mattywausb/ElBanquos_ChristmasLight/Documentation/demo_pictures/01_snowman.jpg

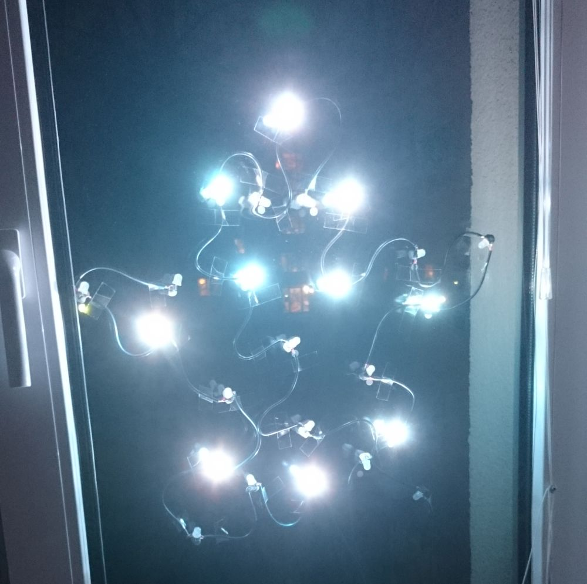
Documentation/demo_pictures/01_snowman.jpg
