mattywausb/ElBanquos_ChristmasLight/Documentation/demo_pictures/02_tree.jpg

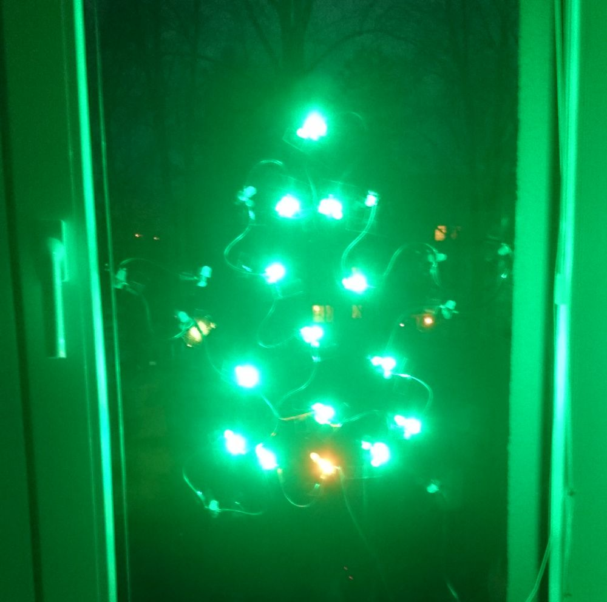
Documentation/demo_pictures/02_tree.jpg
