mattywausb/ElBanquos_ChristmasLight/Documentation/demo_pictures/03_star.jpg

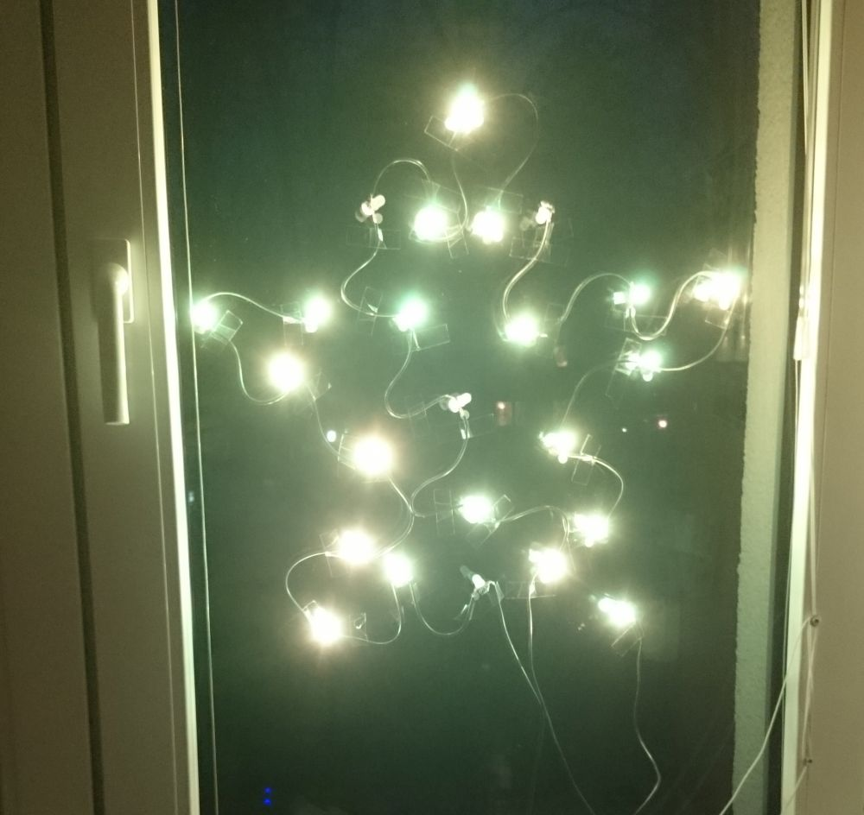
Documentation/demo_pictures/03_star.jpg
