mattywausb/ElBanquos_ChristmasLight/Documentation/demo_pictures/04_heart.jpg

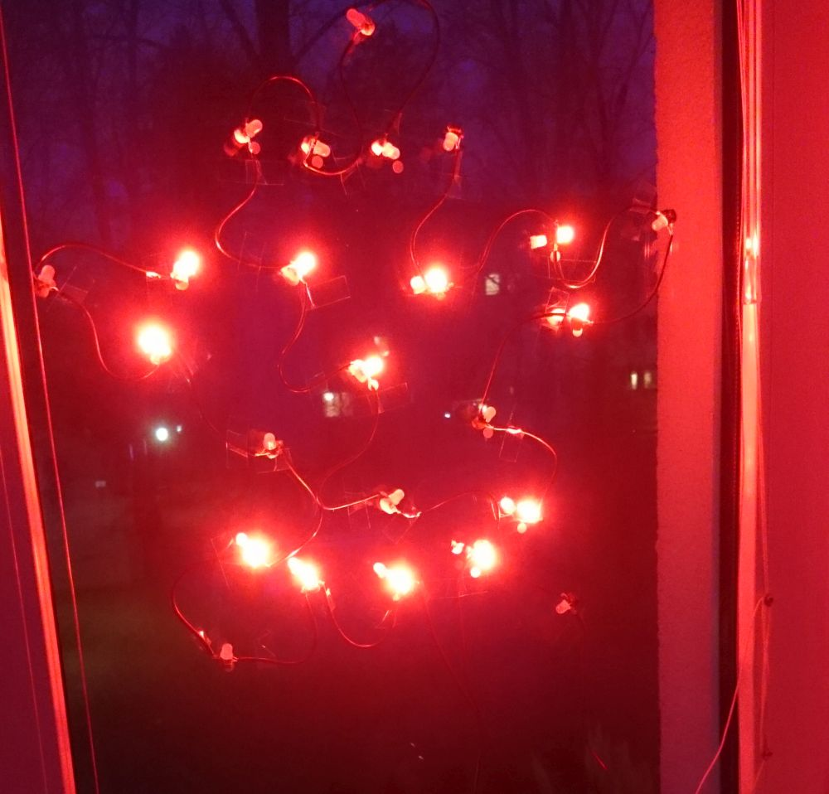
Documentation/demo_pictures/04_heart.jpg
