mattywausb/ElBanquos_ChristmasLight/Documentation/lampArrangement.png

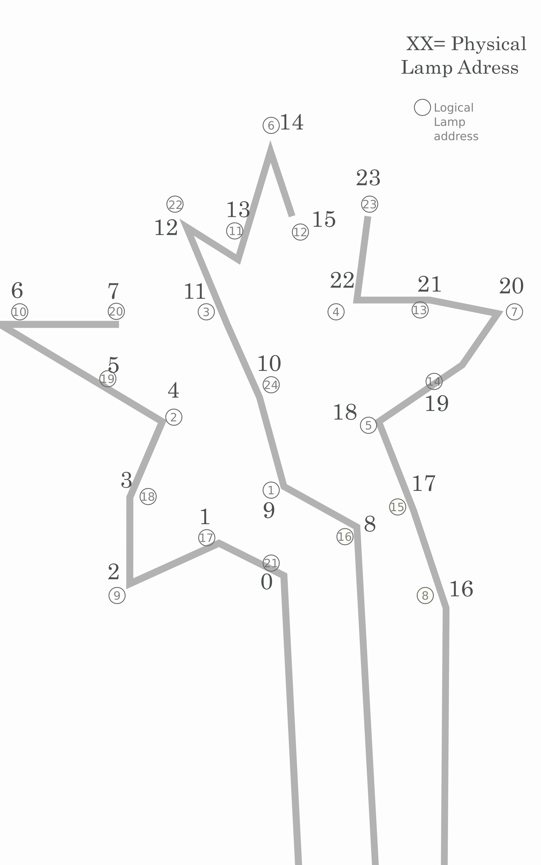
Documentation/lampArrangement.png
