mattywausb/ElBanquos_ChristmasLight/Documentation/build_pictures/02_multicore_cables_from_pc_junkyard.jpg

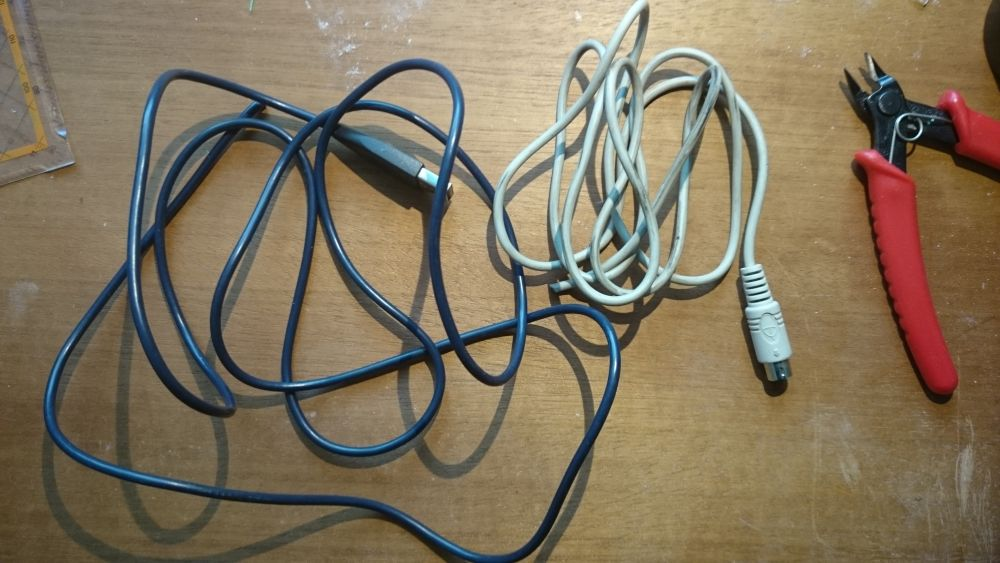
Documentation/build_pictures/02_multicore_cables_from_pc_junkyard.jpg
