mattywausb/ElBanquos_ChristmasLight/Documentation/build_pictures/05_final_wire_element.jpg

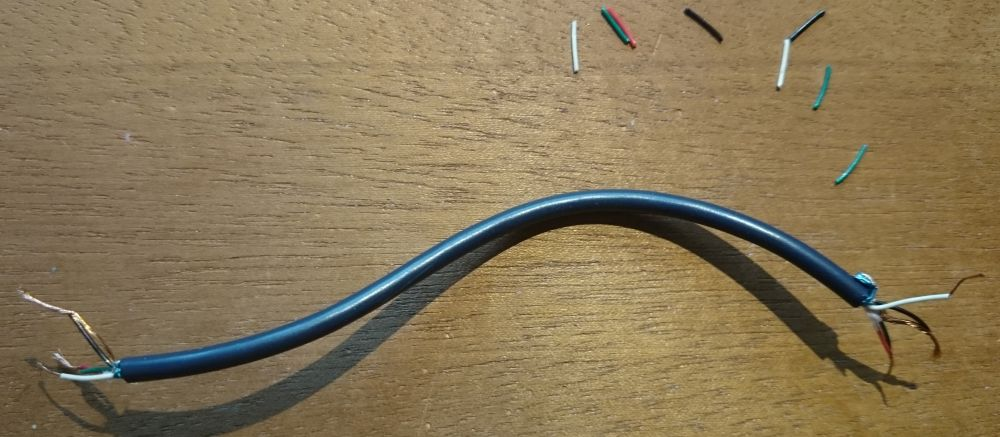
Documentation/build_pictures/05_final_wire_element.jpg
