mattywausb/ElBanquos_ChristmasLight/Documentation/build_pictures/06_ready_to_mount.jpg

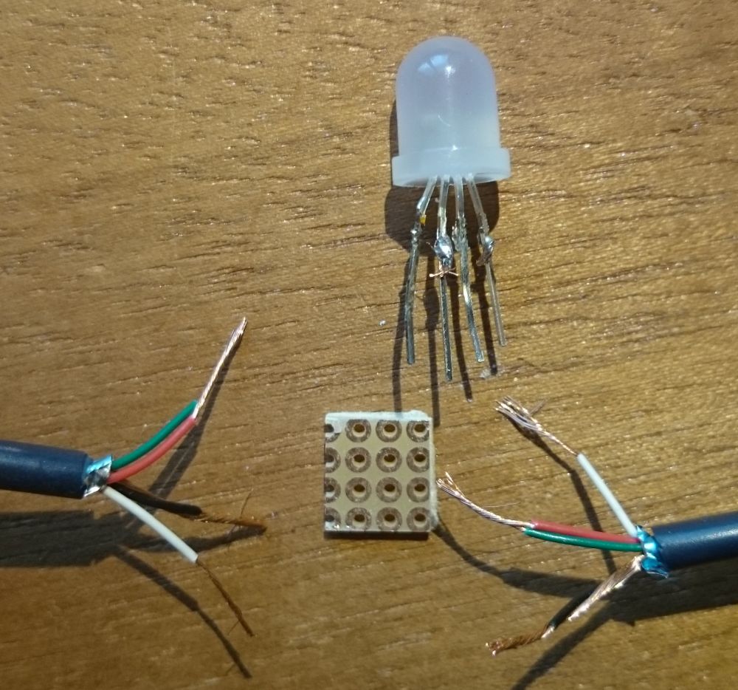
Documentation/build_pictures/06_ready_to_mount.jpg
