mattywausb/ElBanquos_ChristmasLight/Documentation/build_pictures/07_wires_first.jpg

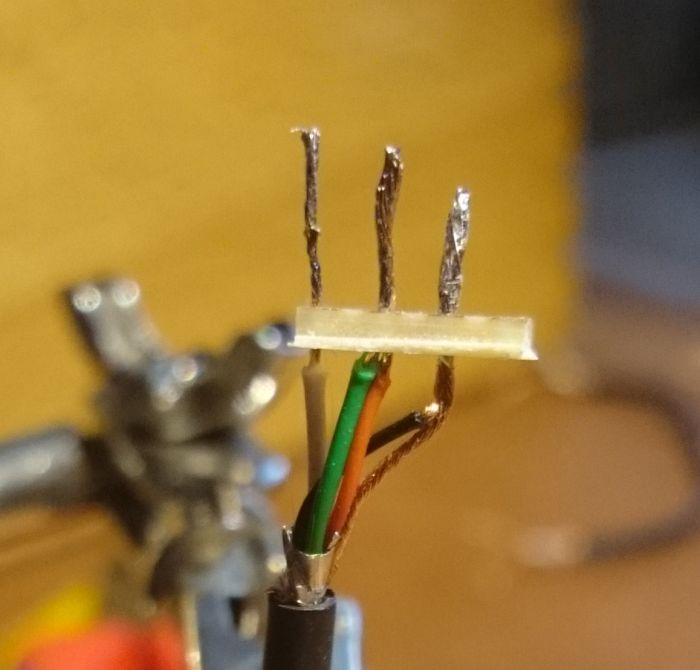
Documentation/build_pictures/07_wires_first.jpg
