mattywausb/ElBanquos_ChristmasLight/Documentation/build_pictures/08_wires_first_b.jpg

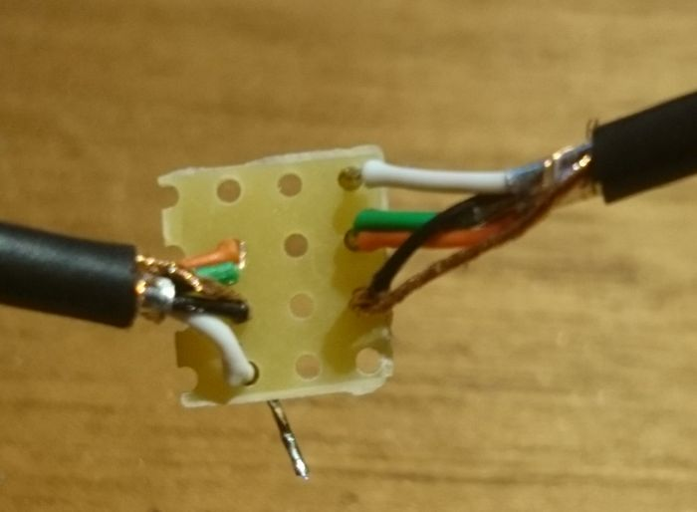
Documentation/build_pictures/08_wires_first_b.jpg
