mattywausb/ElBanquos_ChristmasLight/Documentation/build_pictures/09_bended_led_contacts.jpg

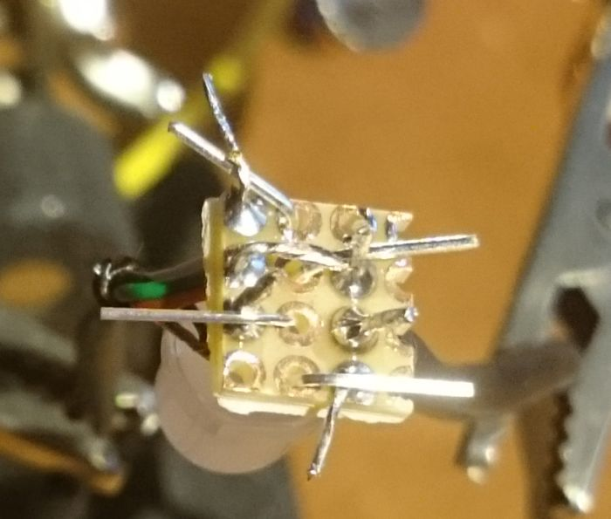
Documentation/build_pictures/09_bended_led_contacts.jpg
