mattywausb/ElBanquos_ChristmasLight/Documentation/build_pictures/10_solded_lamp.jpg

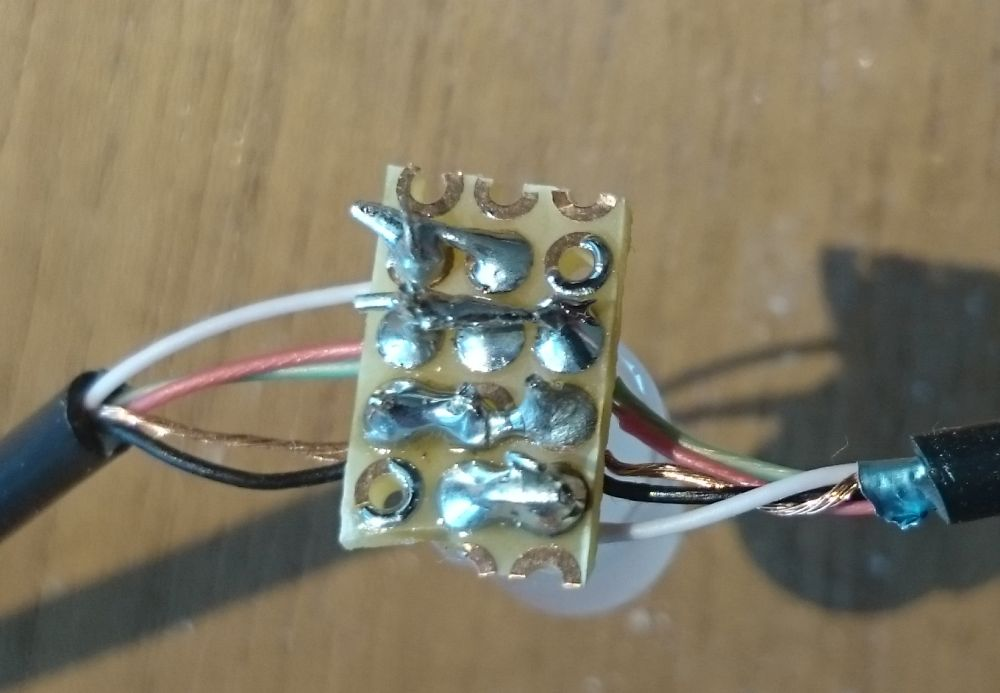
Documentation/build_pictures/10_solded_lamp.jpg
