mattywausb/ElBanquos_ChristmasLight/Documentation/build_pictures/11_final_lamp_element.jpg

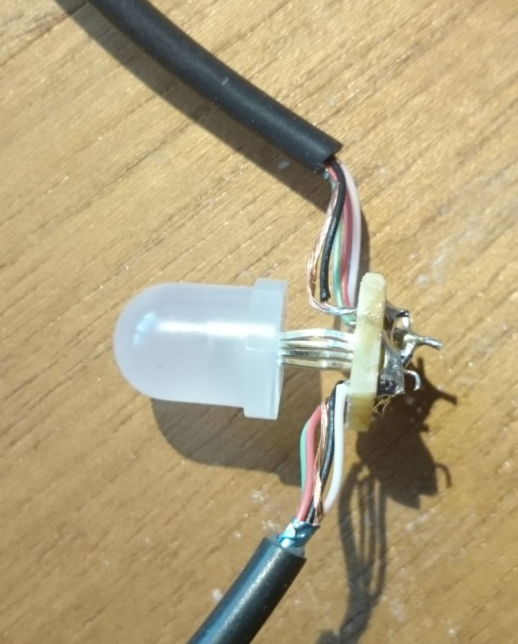
Documentation/build_pictures/11_final_lamp_element.jpg
