mattywausb/ElBanquos_ChristmasLight/Documentation/build_pictures/12_lamp_with_sugru_protection.jpg

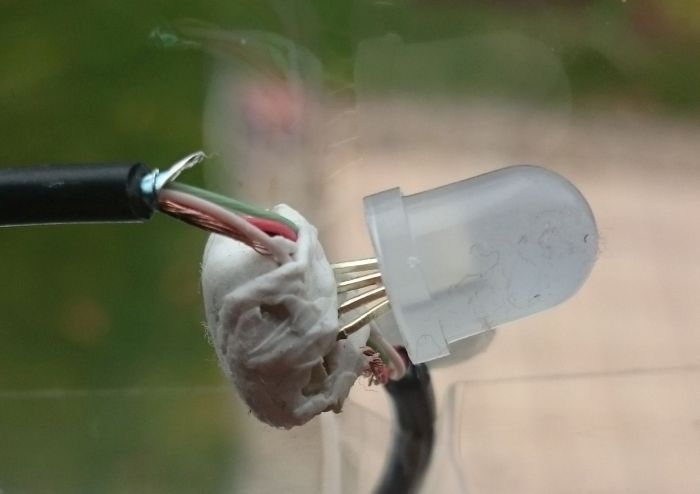
Documentation/build_pictures/12_lamp_with_sugru_protection.jpg
