mattywausb/ElBanquos_ChristmasLight/Documentation/build_pictures/13_cable_plug_a.jpg

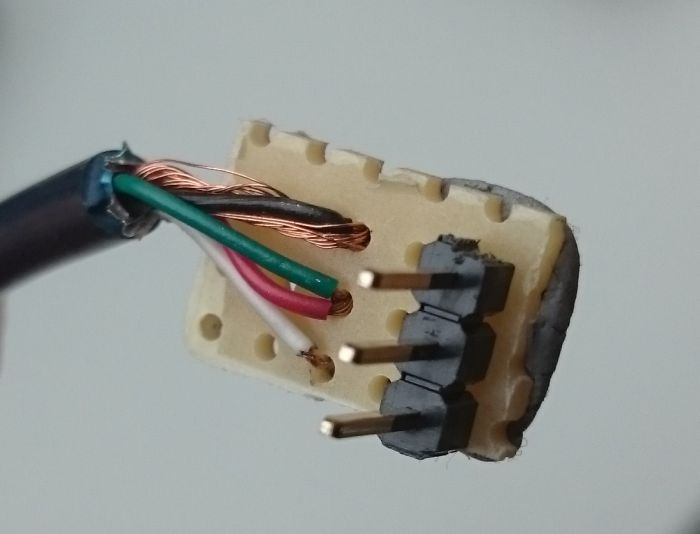
Documentation/build_pictures/13_cable_plug_a.jpg
