mattywausb/ElBanquos_ChristmasLight/Documentation/build_pictures/15_the_uno_board.jpg

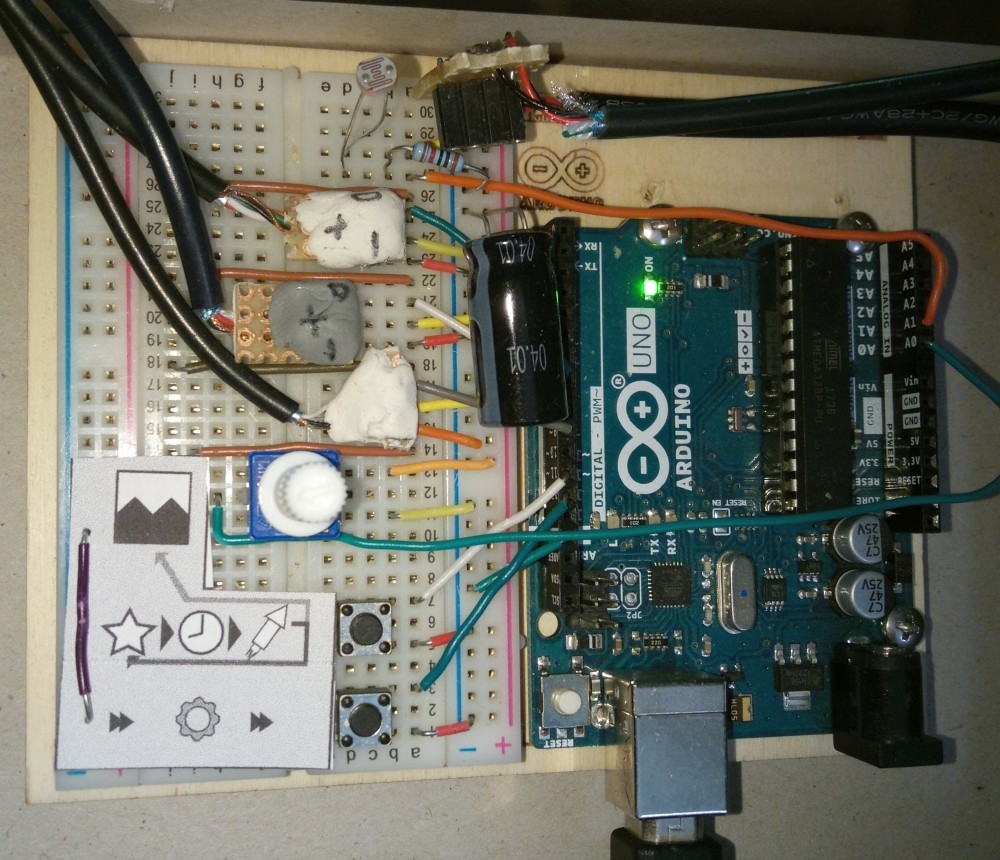
Documentation/build_pictures/15_the_uno_board.jpg
