mattywausb/ElBanquos_ChristmasLight/Documentation/build_pictures/16_PCB_front.jpg

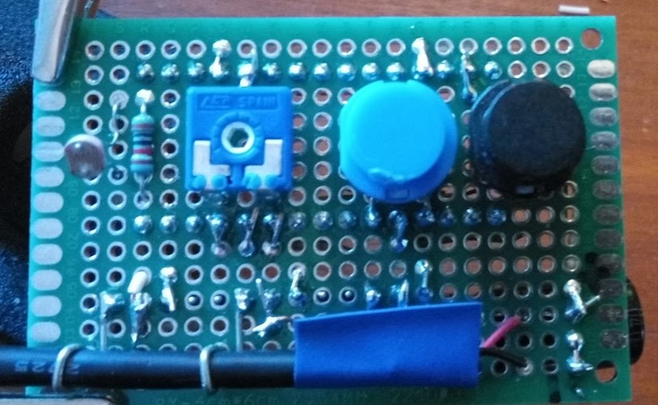
Documentation/build_pictures/16_PCB_front.jpg
