mattywausb/ElBanquos_ChristmasLight/Documentation/build_pictures/17_PCB_back.jpg

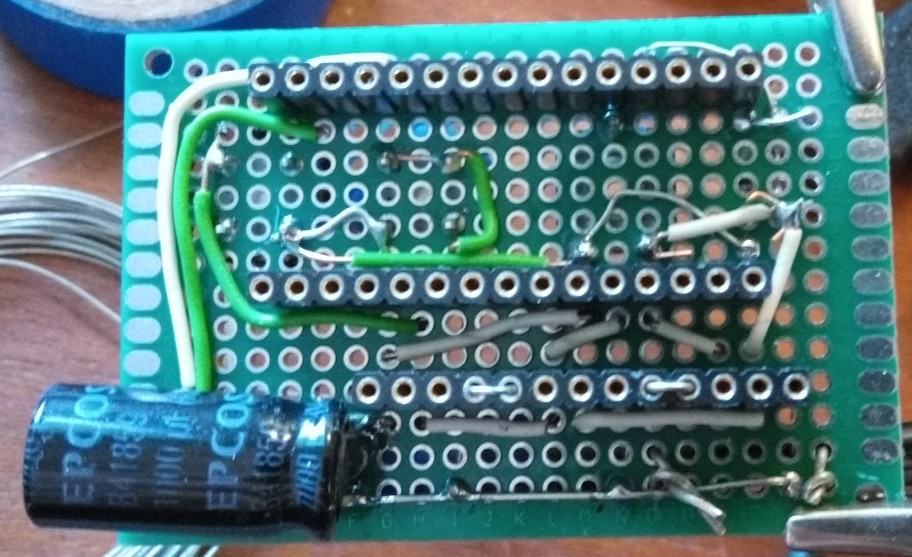
Documentation/build_pictures/17_PCB_back.jpg
