mattywausb/ElBanquos_ChristmasLight/Documentation/build_pictures/18_PCB_back_fully_plugged.jpg

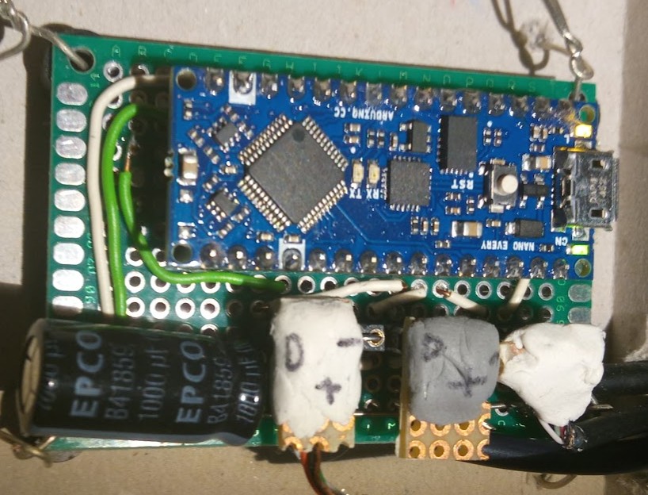
Documentation/build_pictures/18_PCB_back_fully_plugged.jpg
