mattywausb/ElBanquos_ChristmasLight/Arduino/ChistmasLights/input.ino

/* Functions to handle all input elements */

#include "mainSettings.h"

// Activate general trace output

#ifdef TRACE_ON
//#define TRACE_INPUT 
//#define TRACE_INPUT_LIGHTSENSOR
//#define TRACE_INPUT_HIGH
//#define TRACE_INPUT_TIMING 
#endif



/* Button constants */ 
const byte switch_pin_list[] = {3,    // Mode 
                                2    // Step
                               };
                                
#define INPUT_PORT_COUNT sizeof(switch_pin_list)

#define INPUT_BUTTON_COOLDOWN 10   // Milliseconds until we accept another state change of the buttons



/* Button variables */

unsigned long buttons_last_read_time=0;  // Millis of last butto ncheck
unsigned int button_raw_state=0;         // state of buttons in last button check
unsigned int button_tick_state = 0;      // current and historized state in the actual tick



/* Generic button bit pattern (Button 0) */

#define INPUT_0_BITS 0x0003
#define INPUT_0_IS_ON_PATTERN 0x0003
#define INPUT_0_SWITCHED_ON_PATTERN 0x0001
#define INPUT_0_SWITCHED_OFF_PATTERN 0x0002


/* Element specific  button bit pattern */
/*                                         76543210 */

#define INPUT_BUTTON_A_BITS              0x0003
#define INPUT_BUTTON_A_IS_PRESSED_PATTERN   0x0003
#define INPUT_BUTTON_A_GOT_PRESSED_PATTERN   0x0001
#define INPUT_BUTTON_A_GOT_RELEASED_PATTERN  0x0002


#define INPUT_BUTTON_B_BITS                  0x000c
#define INPUT_BUTTON_B_IS_PRESSED_PATTERN    0x000c
#define INPUT_BUTTON_B_GOT_PRESSED_PATTERN   0x0004
#define INPUT_BUTTON_B_GOT_RELEASED_PATTERN  0x0008

#define INPUT_ALL_BUTTON_STATE_MASK 0x000f


/* history handling */

#define INPUT_CURRENT_BITS 0x0005
#define INPUT_PREVIOUS_BITS 0x000a


unsigned long last_press_start_time=0;
unsigned long last_press_end_time=0;
bool input_enabled=true;

/* Light Sensor */

// Porst are dfined in main settings


#define INPUT_HISTERESYS_GAP 50
#define INPUT_THRESHOLD_BASE INPUT_HISTERESYS_GAP+3
#define INPUT_NOISE_TOLERANCE 3

byte input_daylight=0;

int input_normalized_light_sensor_value=0;
int input_light_sensor_value_denoised=0;
int input_threshold_base_value_denoised=0;

/* General state variables */
volatile bool setupComplete = false;
unsigned long input_last_change_time = 0;



/* ********************************************************************************************************** */
/*               Interface functions                                                                          */

/* ------------- General Information --------------- */

int input_getSecondsSinceLastEvent() {
  unsigned long timestamp_difference = (millis() - input_last_change_time) / 1000;
  if (timestamp_difference > 255) return 255;
#ifdef TRACE_INPUT_TIMING
  Serial.print(F("TRACE_INPUT_TIMING:input last interaction:"));
  Serial.println(timestamp_difference);
#endif
  return timestamp_difference;
}

/* ------------- Button events --------------- */

bool input_modeGotPressed()
{

  return input_enabled && ((button_tick_state & INPUT_BUTTON_A_BITS) == INPUT_BUTTON_A_GOT_PRESSED_PATTERN);
}

bool input_modeIsPressed()
{
  return input_enabled && ((button_tick_state & INPUT_BUTTON_A_BITS) == INPUT_BUTTON_A_IS_PRESSED_PATTERN); 
}

byte input_modeGotReleased()
{
  return input_enabled && ((button_tick_state & INPUT_BUTTON_A_BITS) == INPUT_BUTTON_A_GOT_RELEASED_PATTERN); 
}

bool input_stepGotPressed()
{

  return input_enabled && ((button_tick_state & INPUT_BUTTON_B_BITS) == INPUT_BUTTON_B_GOT_PRESSED_PATTERN);
}

bool input_stepIsPressed()
{
  return input_enabled && ((button_tick_state & INPUT_BUTTON_B_BITS) == INPUT_BUTTON_B_IS_PRESSED_PATTERN); 
}

byte input_stepGotReleased()
{
  return input_enabled && ((button_tick_state & INPUT_BUTTON_B_BITS) == INPUT_BUTTON_B_GOT_RELEASED_PATTERN); 
}

long input_getCurrentPressDuration()
{
  #ifdef TRACE_INPUT_TIMING
    Serial.print(F("TRACE_INPUT_TIMING:input CurrentPressDuration:"));
    Serial.println(millis()-last_press_start_time);
  #endif
    
  return millis()-last_press_start_time;
}

long input_getLastPressDuration()
{
  return  last_press_end_time-last_press_start_time;
}


/* ------------- Operations ----------------- */



/* Disable input until all buttons have been released */

void input_IgnoreUntilRelease()
{
  input_enabled=false;
}


byte input_getDaylightState()
{
  input_determine_normalized_light_sensor_value();
  if(input_normalized_light_sensor_value>1) input_daylight=1;
  if(input_normalized_light_sensor_value<-1) input_daylight=0;
  return input_daylight;
}


int input_get_normalized_light_sensor_value()
{
  input_determine_normalized_light_sensor_value();
  return input_normalized_light_sensor_value;
  
}


/* *************************** internal implementation *************************** */

void input_determine_normalized_light_sensor_value()
{
  #ifdef TRACE_INPUT_LIGHTSENSOR
    char stringBuffer[30];
  #endif
  int sensor_value=analogRead(INPUT_ANALOG_PORT_SENSOR);
  int threshold_base_value=analogRead(INPUT_ANALOG_PORT_THRESHOLD)+INPUT_THRESHOLD_BASE;

  if(abs(input_light_sensor_value_denoised-sensor_value)>=INPUT_NOISE_TOLERANCE)input_light_sensor_value_denoised=sensor_value;
  if(abs(input_threshold_base_value_denoised-threshold_base_value)>=INPUT_NOISE_TOLERANCE)input_threshold_base_value_denoised=threshold_base_value;

  input_normalized_light_sensor_value=(input_light_sensor_value_denoised-input_threshold_base_value_denoised)/INPUT_HISTERESYS_GAP;
  #ifdef TRACE_INPUT_LIGHTSENSOR
      Serial.print(F("TRACE_INPUT_LIGHTSENSOR"));
      sprintf(stringBuffer,"s=%5d t=%5d nlv=%2d\n",input_light_sensor_value_denoised,input_threshold_base_value_denoised,input_normalized_light_sensor_value);
      Serial.print(stringBuffer);
  #endif      
}



/* ************************************* TICK ***********************************************
   translate the state of buttons into the ticks of the master loop
   Must be called by the master loop for every cycle to provide valid event states of
   all input devices.
   Also transfers state changes, tracked with the timer interrupt into a tick state
*/

void input_switches_scan_tick()
{
  bool change_happened=false;
  
  /* regular button scan and encoder crosscheck */
  if (millis() - buttons_last_read_time > INPUT_BUTTON_COOLDOWN)
  {
    byte isPressed=0;
    int analog_value=0;
    buttons_last_read_time = millis();
    
    for (int i = 0; i <INPUT_PORT_COUNT; i++) { // for all input ports configured
      isPressed=!digitalRead(switch_pin_list[i]);
      bitWrite(button_raw_state,i*2,isPressed);
    }

  }

  /* copy previous tick  state to history bits  and take raw pattern as new value */
  button_tick_state = (button_tick_state & INPUT_CURRENT_BITS) << 1
               | (button_raw_state & INPUT_CURRENT_BITS);

  
  /* Track pressing time */
  for (int i =0;i<INPUT_PORT_COUNT;i++)
  {
    if((button_tick_state & (INPUT_0_BITS<<(i*2))) == INPUT_0_SWITCHED_ON_PATTERN<<(i*2)) 
    {
      change_happened=true;
      last_press_end_time =last_press_start_time=millis();
      #ifdef TRACE_INPUT_HIGH
        Serial.print(("TRACE_INPUT_HIGH:press of "));Serial.println(i);
      #endif     
    }
    if((button_tick_state & (INPUT_0_BITS<<(i*2))) == INPUT_0_SWITCHED_OFF_PATTERN<<(i*2)) 
    {
      last_press_end_time=millis();
      change_happened=true;
      #ifdef TRACE_INPUT_HIGH
        Serial.print(("TRACE_INPUT_HIGH:release of "));Serial.println(i);
      #endif     
    }
  }

  if((button_tick_state & INPUT_ALL_BUTTON_STATE_MASK) ==0x00)  input_enabled=true; // enable input when all is released and settled

  if(change_happened)input_last_change_time = millis(); // Reset the globel age of interaction


} // void input_switches_tick()




/* ***************************       S E T U P           ******************************
*/

void input_setup() {

  /* Initialize switch pins and raw_state_register array */
  for (byte switchIndex = 0; switchIndex < INPUT_PORT_COUNT ; switchIndex++) {
    pinMode(switch_pin_list[switchIndex], INPUT_PULLUP);
  }

  setupComplete = true;
}
