mattywausb/ElBanquos_ChristmasLight/Arduino/ChistmasLights/mainSettings.h

//#define TRACE_ON 


// need this here to provide definition also in ChristmasLights.ino
#define INPUT_ANALOG_PORT_THRESHOLD 1
#define INPUT_ANALOG_PORT_SENSOR 0

void output_setLightColor(byte index,int red,int green, int blue);
